dragonlock2/STM32_APRS/Core/Src/APRS.c

/*
 * APRS.c
 *
 *  Created on: Jul 15, 2020
 *      Author: matthewtran
 */

#include "APRS.h"

const uint16_t APRS_CCITT_LOOKUP[256] = {
	0x0000, 0x1189, 0x2312, 0x329b, 0x4624, 0x57ad, 0x6536, 0x74bf,
	0x8c48, 0x9dc1, 0xaf5a, 0xbed3, 0xca6c, 0xdbe5, 0xe97e, 0xf8f7,
	0x1081, 0x0108, 0x3393, 0x221a, 0x56a5, 0x472c, 0x75b7, 0x643e,
	0x9cc9, 0x8d40, 0xbfdb, 0xae52, 0xdaed, 0xcb64, 0xf9ff, 0xe876,
	0x2102, 0x308b, 0x0210, 0x1399, 0x6726, 0x76af, 0x4434, 0x55bd,
	0xad4a, 0xbcc3, 0x8e58, 0x9fd1, 0xeb6e, 0xfae7, 0xc87c, 0xd9f5,
	0x3183, 0x200a, 0x1291, 0x0318, 0x77a7, 0x662e, 0x54b5, 0x453c,
	0xbdcb, 0xac42, 0x9ed9, 0x8f50, 0xfbef, 0xea66, 0xd8fd, 0xc974,
	0x4204, 0x538d, 0x6116, 0x709f, 0x0420, 0x15a9, 0x2732, 0x36bb,
	0xce4c, 0xdfc5, 0xed5e, 0xfcd7, 0x8868, 0x99e1, 0xab7a, 0xbaf3,
	0x5285, 0x430c, 0x7197, 0x601e, 0x14a1, 0x0528, 0x37b3, 0x263a,
	0xdecd, 0xcf44, 0xfddf, 0xec56, 0x98e9, 0x8960, 0xbbfb, 0xaa72,
	0x6306, 0x728f, 0x4014, 0x519d, 0x2522, 0x34ab, 0x0630, 0x17b9,
	0xef4e, 0xfec7, 0xcc5c, 0xddd5, 0xa96a, 0xb8e3, 0x8a78, 0x9bf1,
	0x7387, 0x620e, 0x5095, 0x411c, 0x35a3, 0x242a, 0x16b1, 0x0738,
	0xffcf, 0xee46, 0xdcdd, 0xcd54, 0xb9eb, 0xa862, 0x9af9, 0x8b70,
	0x8408, 0x9581, 0xa71a, 0xb693, 0xc22c, 0xd3a5, 0xe13e, 0xf0b7,
	0x0840, 0x19c9, 0x2b52, 0x3adb, 0x4e64, 0x5fed, 0x6d76, 0x7cff,
	0x9489, 0x8500, 0xb79b, 0xa612, 0xd2ad, 0xc324, 0xf1bf, 0xe036,
	0x18c1, 0x0948, 0x3bd3, 0x2a5a, 0x5ee5, 0x4f6c, 0x7df7, 0x6c7e,
	0xa50a, 0xb483, 0x8618, 0x9791, 0xe32e, 0xf2a7, 0xc03c, 0xd1b5,
	0x2942, 0x38cb, 0x0a50, 0x1bd9, 0x6f66, 0x7eef, 0x4c74, 0x5dfd,
	0xb58b, 0xa402, 0x9699, 0x8710, 0xf3af, 0xe226, 0xd0bd, 0xc134,
	0x39c3, 0x284a, 0x1ad1, 0x0b58, 0x7fe7, 0x6e6e, 0x5cf5, 0x4d7c,
	0xc60c, 0xd785, 0xe51e, 0xf497, 0x8028, 0x91a1, 0xa33a, 0xb2b3,
	0x4a44, 0x5bcd, 0x6956, 0x78df, 0x0c60, 0x1de9, 0x2f72, 0x3efb,
	0xd68d, 0xc704, 0xf59f, 0xe416, 0x90a9, 0x8120, 0xb3bb, 0xa232,
	0x5ac5, 0x4b4c, 0x79d7, 0x685e, 0x1ce1, 0x0d68, 0x3ff3, 0x2e7a,
	0xe70e, 0xf687, 0xc41c, 0xd595, 0xa12a, 0xb0a3, 0x8238, 0x93b1,
	0x6b46, 0x7acf, 0x4854, 0x59dd, 0x2d62, 0x3ceb, 0x0e70, 0x1ff9,
	0xf78f, 0xe606, 0xd49d, 0xc514, 0xb1ab, 0xa022, 0x92b9, 0x8330,
	0x7bc7, 0x6a4e, 0x58d5, 0x495c, 0x3de3, 0x2c6a, 0x1ef1, 0x0f78
};

APRSPacket APRS_DEFAULT_PACKET = {
	.dest     = "APCAL",
	.callsign = "KN6IEK-1",
	.digi     = "WIDE1-1,WIDE2-2",
	.info     = ">Hola Universe!"
};

// variables
static uint8_t decoded_bits_buff[APRS_FIFO_BYTES]; // don't need this much, just lazy
static BitFIFO decoded_bits;
static uint32_t decoded_bits_len;
static uint8_t ones_seen;
static bool gathering;

// global variables
APRSPacket APRS_decoded_packet;
bool APRS_decoded_packet_valid;

// public functions
void APRS_init() {
	APRS_decoded_packet.dest = malloc(APRS_SIGN_LEN);
	APRS_decoded_packet.callsign = malloc(APRS_SIGN_LEN);
	APRS_decoded_packet.digi = malloc(APRS_SIGN_LEN * APRS_MAX_DIGI);
	APRS_decoded_packet.info = malloc(APRS_MAX_INFO + 1);
	APRS_decoded_packet_valid = 0;

	BitFIFO_init(&decoded_bits, decoded_bits_buff, sizeof(decoded_bits_buff));
	decoded_bits_len = 0;
	ones_seen = 0;
	gathering = false;
}

void APRS_print(APRSPacket *pack) {
	printf("DEST: %s | SRC: %s | DIGI: %s | %s\r\n", pack->dest, pack->callsign, pack->digi, pack->info);
}

void APRS_encode(BitFIFO *bfifo, APRSPacket *pack) {
	if (strlen(pack->info) > 256) {
		Error_Handler();
	}

	for (uint8_t i = 0; i < (APRS_PREFLAGS + 1); i++) { // preflags
		APRS_encode_insert_byte(bfifo, 0b10000000);
	}
	uint8_t stuff_count = 0;
	uint16_t crc = 0xFFFF;
	bool curr_nrzi = true;

	APRS_encode_insert_callsign(bfifo, pack->dest, &stuff_count, &curr_nrzi, &crc, 0); // destination
	APRS_encode_insert_callsign(bfifo, pack->callsign, &stuff_count, &curr_nrzi, &crc, 0); // callsign

	// assumes at least 1 digipeater
	char *digi = pack->digi;
	uint32_t digidex = 0;
	uint8_t digiend = 0;
	while (!digiend) {
		while (digi[digidex] >= '-') { // assumes ',' delimiter
			digidex++;
		}
		if (digi[digidex] == 0) { // reached end
			digiend = 1;
		}
		APRS_encode_insert_callsign(bfifo, digi, &stuff_count, &curr_nrzi, &crc, digiend);
		digi += digidex + 1;
	}

	APRS_encode_stuff_byte_update_fcs(bfifo, 0x03, &stuff_count, &curr_nrzi, &crc); // control field
	APRS_encode_stuff_byte_update_fcs(bfifo, 0xF0, &stuff_count, &curr_nrzi, &crc); // id

	for (uint16_t i = 0; i < strlen(pack->info); i++) { // info
		APRS_encode_stuff_byte_update_fcs(bfifo, pack->info[i], &stuff_count, &curr_nrzi, &crc);
	}

	crc = ~crc; // don't forget this
	APRS_encode_stuff_byte(bfifo, crc & 0xFF, &stuff_count, &curr_nrzi); // FCS, LSB first
	APRS_encode_stuff_byte(bfifo, crc >> 8, &stuff_count, &curr_nrzi);

	for (uint8_t i = 0; i < (APRS_POSTFLAGS + 1); i++) { // postflags
		APRS_encode_insert_byte(bfifo, curr_nrzi ? 0b10000000 : 0b01111111);
	}
}

void APRS_decode(uint8_t *bites, uint32_t len) {
	// check FCS CRC
	uint16_t crc = 0xFFFF;
	for (uint32_t i = 0; i < len - 2; i++) {
		APRS_update_fcs(bites[i], &crc);
	}
	crc = ~crc;
	if ((bites[len-1] << 8 | bites[len-2]) != crc) {
		return; // bad CRC
	}

	uint32_t i = 0; // starting at digipeater start position
	bool end = 0;

	end = APRS_decode_callsign(bites + i, APRS_decoded_packet.dest);
	i += 7;
	end = APRS_decode_callsign(bites + i, APRS_decoded_packet.callsign);
	i += 7;
	char *digi = APRS_decoded_packet.digi;
	while (!end) {
		end = APRS_decode_callsign(bites + i, digi);
		i += 7;
		while (*digi) { digi++; } // search for '\0' and stop there
		if (!end) {
			*digi++ = ',';
		}
	}
	if (*(bites + i) != 0x03) {
		return; // bad control field
	}
	i++;
	if (*(bites + i) != 0xF0) {
		return; // bad id
	}
	i++;
	char *info = APRS_decoded_packet.info;
	while (i < len - 2) {
		*info = bites[i++];
		info++;
	}
	*info = '\0';

	APRS_decoded_packet_valid = 1;

	APRSGUI_addpack(&APRS_decoded_packet);
}

// private helpers
void APRS_update_fcs(uint8_t b, uint16_t *crc) {
	*crc = ((*crc) >> 8) ^ APRS_CCITT_LOOKUP[((*crc) ^ b) & 0xFF];
}

void APRS_encode_insert_byte(BitFIFO *bfifo, uint8_t b) {
	for (uint8_t i = 0; i < 8; i++) {
		BitFIFO_push(bfifo, b & 0x01); // LSB first
		b >>= 1;
	}
}

void APRS_encode_stuff_byte(BitFIFO *bfifo, uint8_t b, uint8_t *stuff_count, bool *curr_nrzi) {
	for (uint8_t i = 0; i < 8; i++) {
		if (b & 0x01) {
			*stuff_count += 1;
			BitFIFO_push(bfifo, *curr_nrzi); // add 1
		} else {
			*stuff_count = 0;
			BitFIFO_push(bfifo, !*curr_nrzi); // add 0
			*curr_nrzi = !*curr_nrzi;
		}
		if (*stuff_count == 5) {
			*stuff_count = 0;
			BitFIFO_push(bfifo, !*curr_nrzi); // add 0
			*curr_nrzi = !*curr_nrzi;
		}
		b >>= 1;
	}
}

void APRS_encode_stuff_byte_update_fcs(BitFIFO *bfifo, uint8_t b, uint8_t *stuff_count, bool *curr_nrzi, uint16_t *crc) {
	APRS_encode_stuff_byte(bfifo, b, stuff_count, curr_nrzi);
	APRS_update_fcs(b, crc);
}

void APRS_encode_insert_callsign(BitFIFO *bfifo, char *sign, uint8_t *stuff_count, bool *curr_nrzi, uint16_t *crc, bool end) {
	// auto-terminates at ',' or '\0'
	uint8_t c = 0, ssid = 1;
	while (*sign) {
		if (*sign == '-') {
			ssid = 0;
			break;
		}
		APRS_encode_stuff_byte_update_fcs(bfifo, *sign << 1, stuff_count, curr_nrzi, crc);
		c++;
		sign++;
	}
	for (; c < 6; c++) { // pad to 6 bytes
		APRS_encode_stuff_byte_update_fcs(bfifo, ' ' << 1, stuff_count, curr_nrzi, crc);
	}
	if (ssid) {
		ssid = 0;
	} else if (*(sign+2) >= '0') { // assumes ',' delimiter, otherwise need  <= '9' also
		ssid = 10 + (*(sign+2) - '0');
	} else {
		ssid = *(sign+1) - '0';
	}
	APRS_encode_stuff_byte_update_fcs(bfifo, ((0b0110000 | ssid) << 1) | end, stuff_count, curr_nrzi, crc);
}

bool APRS_decode_callsign(uint8_t *bites, char *dest) {
	// dest should reserve at least APRS_SIGN_LEN bytes
	// returns 1 if last callsign
	for (uint32_t i = 0;i < 6; i++) {
		char c = bites[i] >> 1;
		if (c == ' ') {
			break;
		}
		*dest++ = c;
	}
	uint8_t ssid = (bites[6] & 0b00011110) >> 1;
	if (ssid) {
		*dest++ = '-';
		if (ssid >= 10) {
			*dest++ = '1';
		}
		*dest++ = '0' + (ssid % 10);
	}
	*dest = '\0';
	uint8_t end = bites[6] & 0x1;
	return end;
}

void APRS_decode_update(bool bit) {
	if (gathering) {
		if (bit) {
			BitFIFO_push(&decoded_bits, 1);
			decoded_bits_len++;
			ones_seen++;
			if (ones_seen == 6) { // either end flag or too many ones, either way send off the packet
				if (decoded_bits_len >= (APRS_MIN_BITS + 7) && decoded_bits_len % 8 == 7) { // 7 bits extra from flag 0b0111111
					APRS_decode(decoded_bits_buff, decoded_bits_len / 8); // BitFIFO is LSB first, so straightup just grab it
				}
				gathering = false;
				// don't reset ones_seen in case actually a start flag
			}
		} else {
			if (ones_seen != 5) { // ignore stuffed bit
				BitFIFO_push(&decoded_bits, 0);
				decoded_bits_len++;
			}
			ones_seen = 0;
		}
		if (decoded_bits_len >= (APRS_MAX_BITS + 7)) {
			gathering = false;
		}
	} else {
		if (bit) {
			ones_seen++;
			if (ones_seen > 6) { // looking from 1111110 to mark start
				ones_seen = 6;
			}
		} else {
			if (ones_seen == 6) { // found our flag
				BitFIFO_reinit(&decoded_bits);
				decoded_bits_len = 0;
				gathering = true;
			}
			ones_seen = 0;
		}
	}
}
